RobinVonBerg/cic_ffm/report/paper/main.tex

\documentclass[11pt,oneside,headsepline,a4paper,ngerman]{scrreprt}

% PACKAGES
\usepackage{graphicx}              % images
\usepackage{xcolor}                % colors
\usepackage{tabularx}              % tables
\usepackage{scrlayer-scrpage}      % KOMA-Skript
\usepackage{minted}                % code formatting
\usepackage{scrhack}               % suppress deprecation warnings
\usepackage[utf8]{inputenc}        % encoding translation 
\usepackage{csquotes}              % quotations   
\usepackage{isodate}               % dates
\usepackage{makecell}              % format table cells
\usepackage{subcaption}            % figure formatting
\usepackage[ngerman]{babel}        % region specific formatting 
\usepackage[T1]{fontenc}           % font encoding
\usepackage[hidelinks]{hyperref}   % external links
\usepackage[hypcap=false]{caption} % captions
\usepackage[splitrule]{footmisc}   % footnotes
\usepackage[
    backend=biber,
    style=numeric
]{biblatex}                     % manage bibliography
\usepackage[
    a4paper,
    headheight=30pt,
]{geometry}                     % page layout

% VARIABLES
\newcommand{\vcontext}{Softwareprojekt}
\newcommand{\vprof}{Prof. Dr. Ulrich Hoffmann }
\newcommand{\vsubject}{Projektbericht}
\newcommand{\vtitle}{Team Stadt Frankfurt}
\newcommand{\vsubtitle}{Cross Innovation Class 2022}
\newcommand{\vauthor}{Sven Hülsen, Robin von Berg}
\newcommand{\vallauthor}{Sven Hülsen, Robin von Berg, Celina Krug, Moritz Hillen,\\Florian Bucher, Maybritt Braun, Lucas Below}

% STYLE CHANGES
\addtokomafont{pagehead}{\sffamily\color[rgb]{0.15,0.15,0.15}} 
\addtokomafont{pagefoot}{\sffamily\color[rgb]{0.15,0.15,0.15}} 
\addtokomafont{titlehead}{\sffamily} 
\addtokomafont{subject}{\sffamily} 
\addtokomafont{title}{\sffamily} 
\addtokomafont{subtitle}{\sffamily} 
\addtokomafont{author}{\sffamily} 
\addtokomafont{date}{\sffamily} 
\KOMAoptions{toc=indentunnumbered}

% CAPTION MARGIN
\captionsetup{margin=1.5cm}

% MINTED BACKGROUND COLOR
\definecolor{minted-bg}{rgb}{0.97,0.97,0.97}
% MINTED CONFIG
\setminted {
    bgcolor=minted-bg,
    linenos,
    tabsize=2,
    breaklines
}

\setlength{\parindent}{0pt}

% BIB FILE
\addbibresource{sources.bib}

% HEADER
\ihead*{
    \begin{tabular}{l} 
        \vcontext{} \\
        \vsubtitle{}
    \end{tabular}
}

\rohead*{
    \begin{tabular}{r} 
        \vsubject{} \\
        \vauthor{}
    \end{tabular}
}

% FOOTER
\cfoot*{\thepage}

% DOCUMENT START
\begin{document}

\titlehead{\vcontext{}\\\vprof{}}
\subject{\vsubject{}}
\title{\\\vtitle{}}
\subtitle{\vsubtitle{}}
\author{\vallauthor{}}
\date{\today}

\maketitle

\addtocontents{toc}{~\hfill\textbf{Seite}\par}

\tableofcontents

\input{chapters/00_introduction}
\input{chapters/01_project}
\input{chapters/02_task_determination}
\input{chapters/03_technical_implementation}
\input{chapters/04_result}
\input{chapters/05_conclusion}
\input{chapters/06_summary}

% BIBLIOGRAPHY LINEBREAKS
\setcounter{biburlnumpenalty}{8000}

\printbibliography{}

\listoffigures{}

\end{document}
