RobinVonBerg/cic_ffm/report/paper/chapters/02_task_determination.tex

\chapter{Aufgabenverteilung}

    Während der KickOff Veranstaltung haben wir Personen festgelegt die die Rollen der Projektleitung und die der Außenkommunikation übernehmen. Im Laufe des Projekts wurden diese Aufgaben aber auch von anderen Personen übernommen, sei es wegen Krankheit, anderen Abwesenheiten oder wegen der Menge an Aufgaben.

    \begin{table}[H]
        \centering
        \begin{tabularx}{\textwidth}{ | l | X | }
            \hline
                \textbf{Rolle} & \textbf{Person} \\
            \hline
                Projektleiterin & Celina Krug \\ 
            \hline
                Außenkommunikation & Florian Bucher \\ 
            \hline
        \end{tabularx}
        \caption{Übersicht der intern vergebenen Rollen.}
        \label{table:roles}
    \end{table}

    \begin{table}[H]
        \centering
        \begin{tabularx}{\textwidth}{ | l | X | }                
            \hline
                \textbf{Aufgabe} & \textbf{Person(en)} \\
            \hline
                Löten der technischen Komponenten &  \makecell[l]{Robin, Sven,Celina,\\Moritz} \\ 
            \hline
                Bau der Kabel(bäume) &  Robin, Sven, Moritz \\ 
            \hline
                Modellbau des großen Modells & \makecell[l]{May, Lucas, Annika,\\ Sven, Celina, Moritz,\\Robin} \\ 
            \hline
                Modellbau der zwei kleinen Modelle & \makecell[l]{May, Lucas, Annika,\\Sven, Moritz} \\ 
            \hline
                Implementation \& Kalibrierung des Füllstandssensor & Sven \\
            \hline
                Implementation \& Kalibrierung des dTOF-Sensors & Sven \\
            \hline
                Implementation der Main-dTOF & Sven \\
            \hline
                Implementation der Animationen & Robin \\
            \hline
                Implementation der BLE-Kommunikation & Robin \\
            \hline
                Implementation der Main-Receiver \& Main-Transmitter & Robin \\
            \hline
                Vorbereitung \& Präsentieren Abschlussveranstaltung & Celina, May \\
            \hline
                Kommunikation/Absprachen mit den Praxispartnern & Robin, Florian \\
            \hline
                Teilnahme an den CheckIns & Celina \\
            \hline
        \end{tabularx}
        \caption{Retrospektiv: Welche Aufgaben wurden von wem übernommen.}
        \label{table:detailed_task_}
    \end{table}
