RobinVonBerg/cic_ffm/report/paper/media/01_project/pencil_sketch_bin_1.jpg

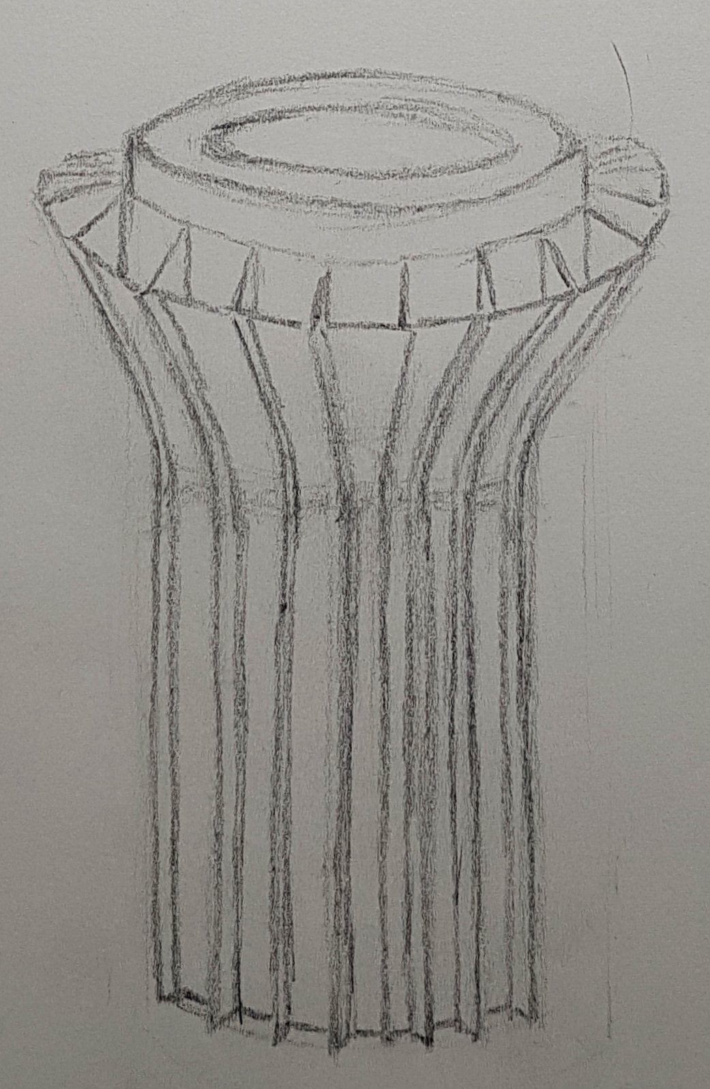
report/paper/media/01_project/pencil_sketch_bin_1.jpg
