RobinVonBerg/cic_ffm/report/paper/media/01_project/WKW_erklaerung.png

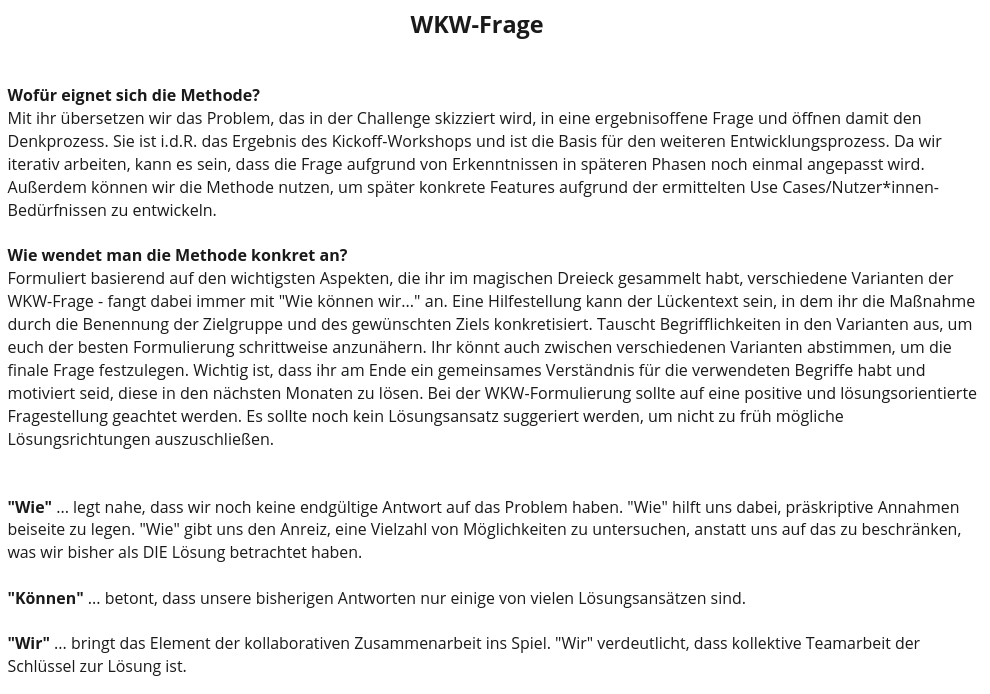
report/paper/media/01_project/WKW_erklaerung.png
