RobinVonBerg/cic_ffm/report/paper/media/01_project/WKW_fragen.png

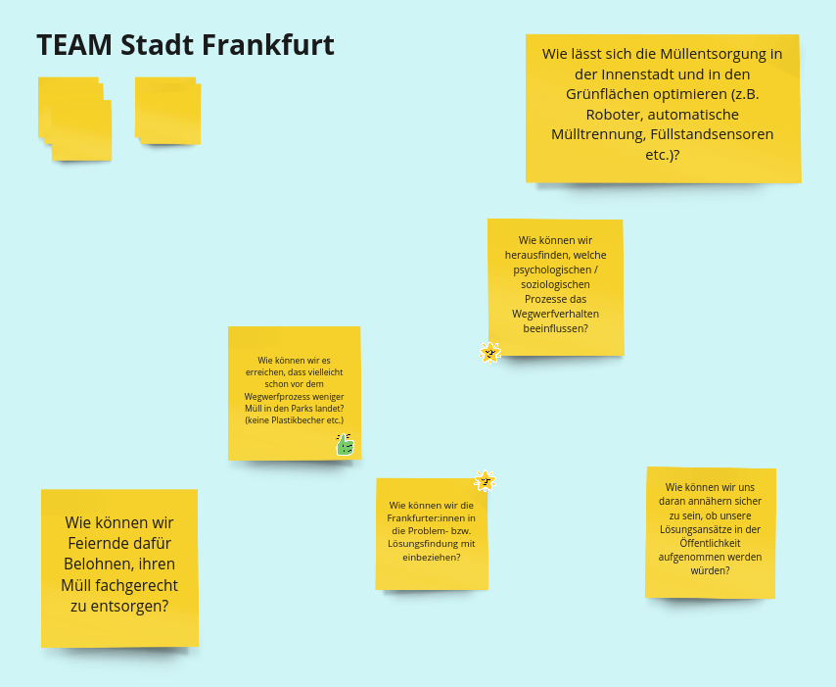
report/paper/media/01_project/WKW_fragen.png
