RobinVonBerg/cic_ffm/report/paper/media/03_technical_implementation/header_2.png

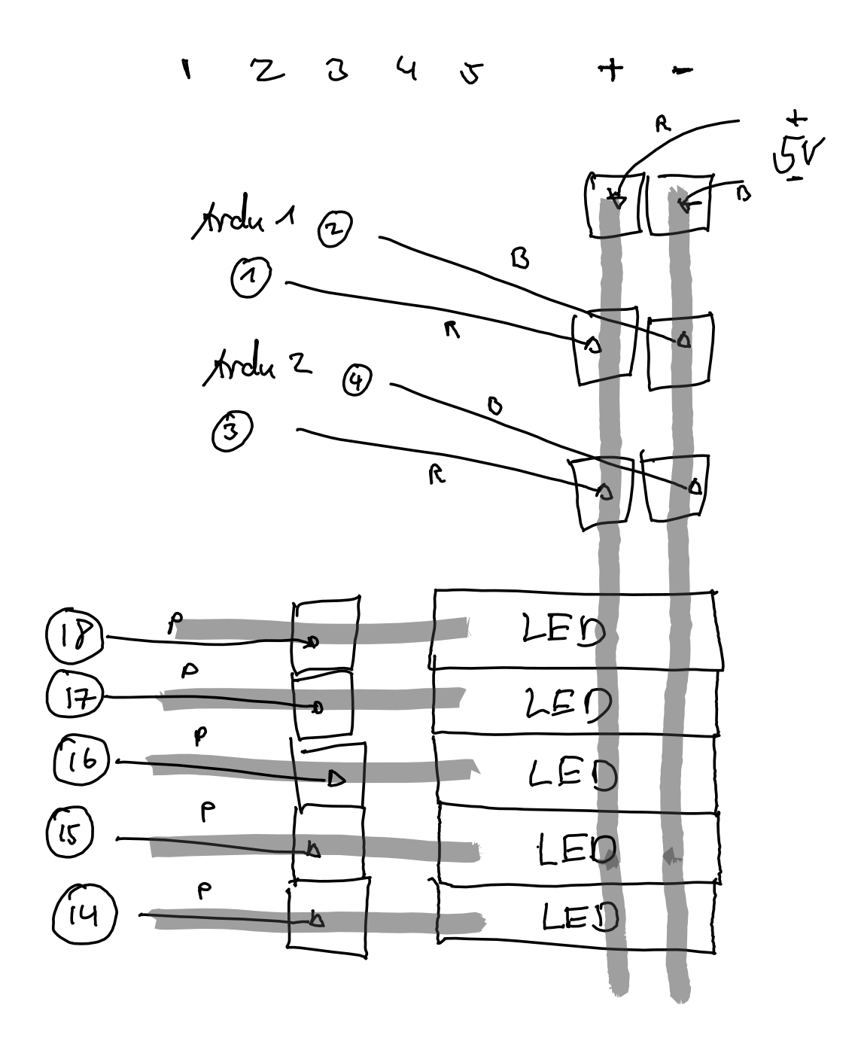
report/paper/media/03_technical_implementation/header_2.png
