RobinVonBerg/cic_ffm/report/paper/media/03_technical_implementation/header_3.png

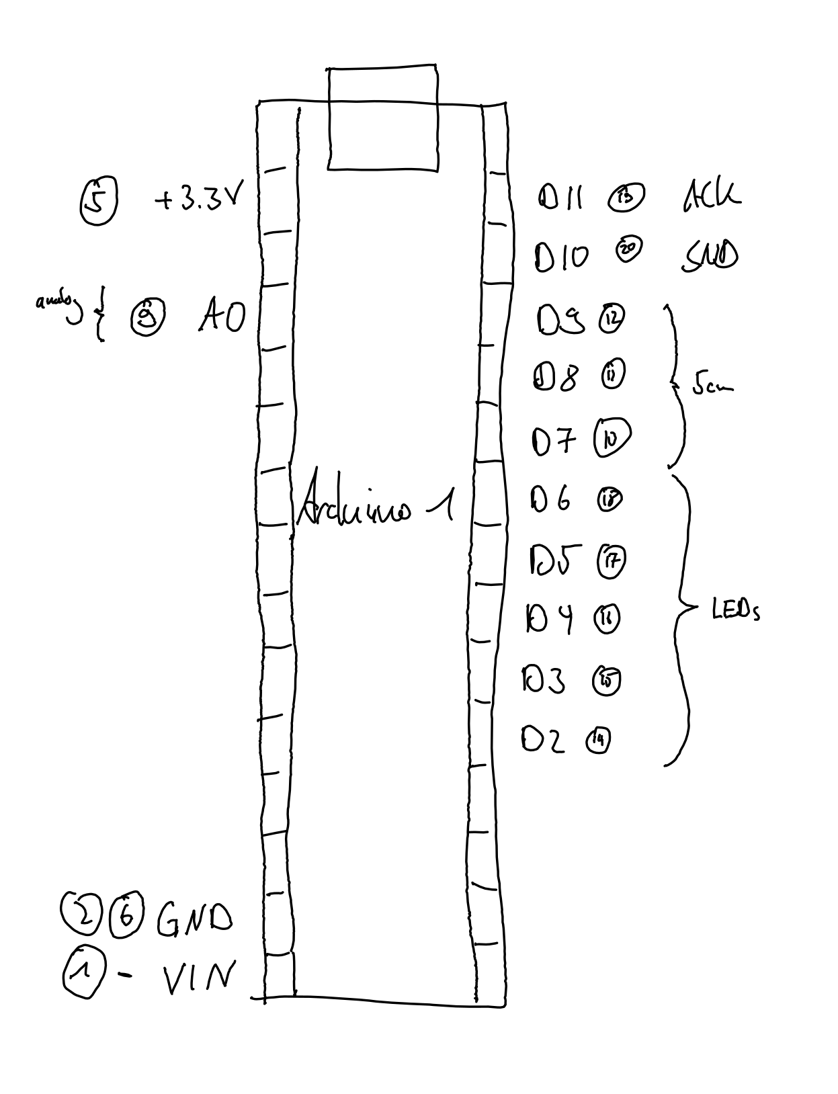
report/paper/media/03_technical_implementation/header_3.png
