RobinVonBerg/cic_ffm/report/paper/media/03_technical_implementation/leds_1.png

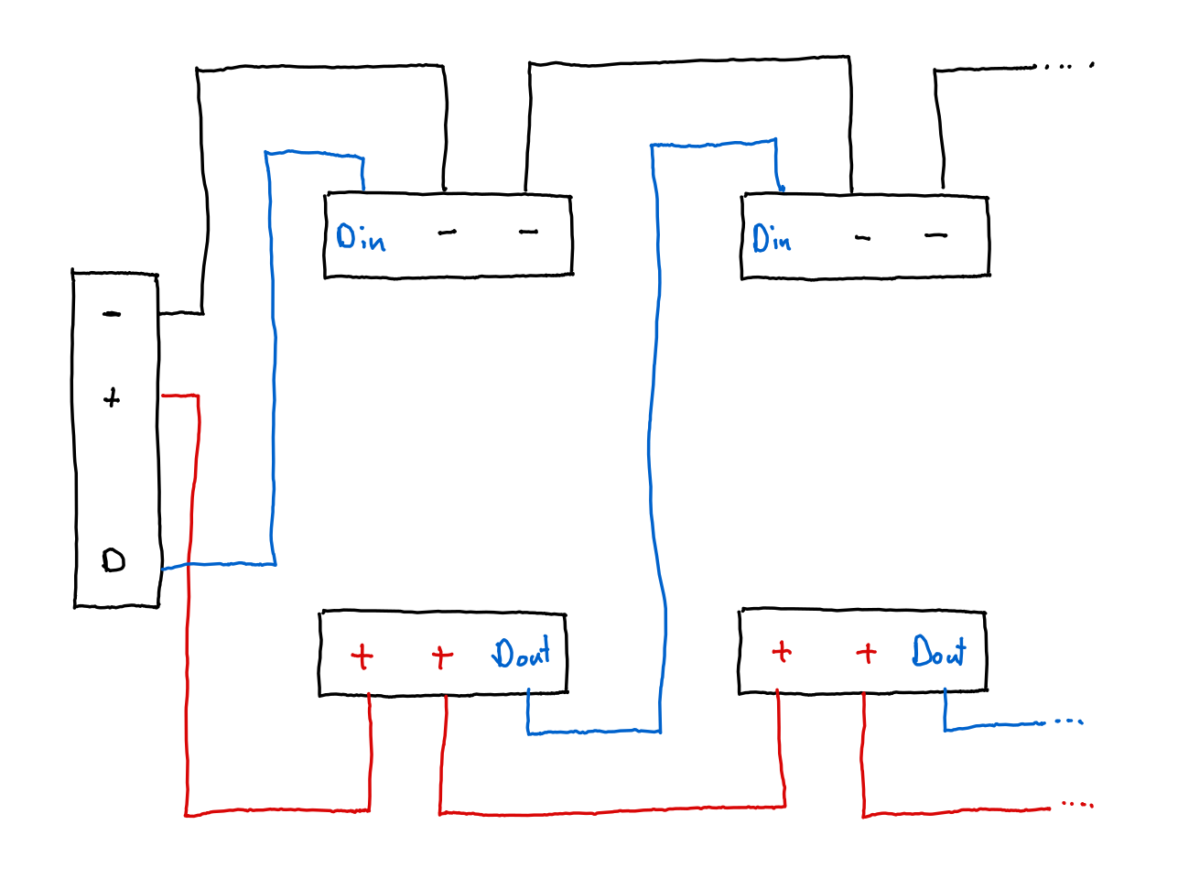
report/paper/media/03_technical_implementation/leds_1.png
