RobinVonBerg/cic_ffm/report/paper/media/03_technical_implementation/sketch_sensor_radius.png

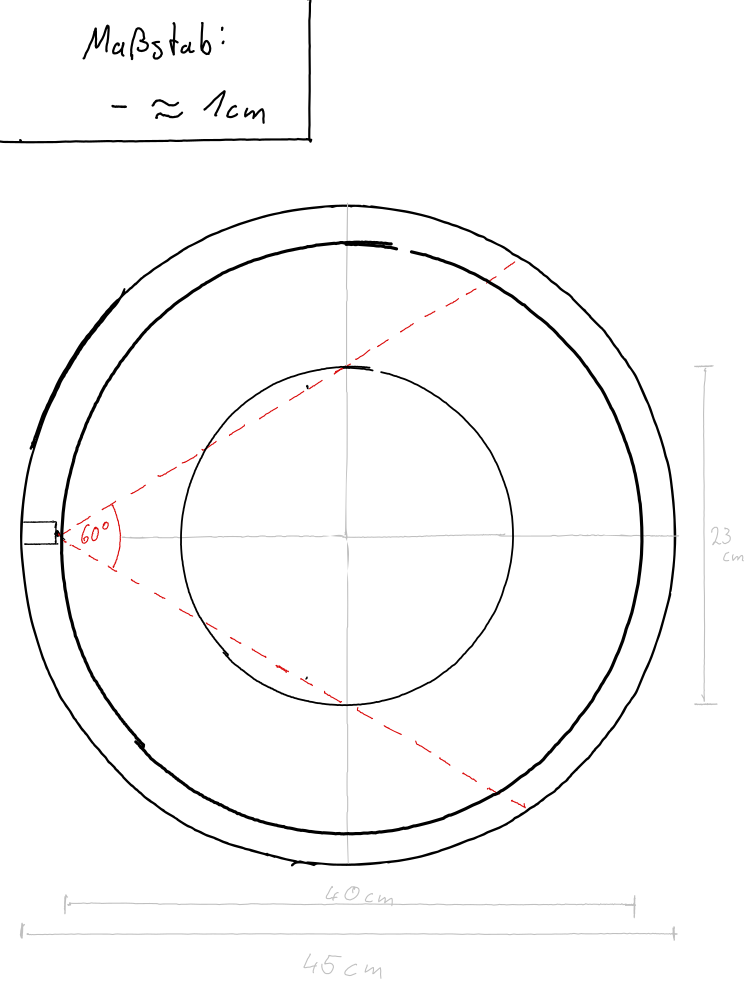
report/paper/media/03_technical_implementation/sketch_sensor_radius.png
