RobinVonBerg/cic_ffm/report/paper/media/04_result/whole_cic.jpg

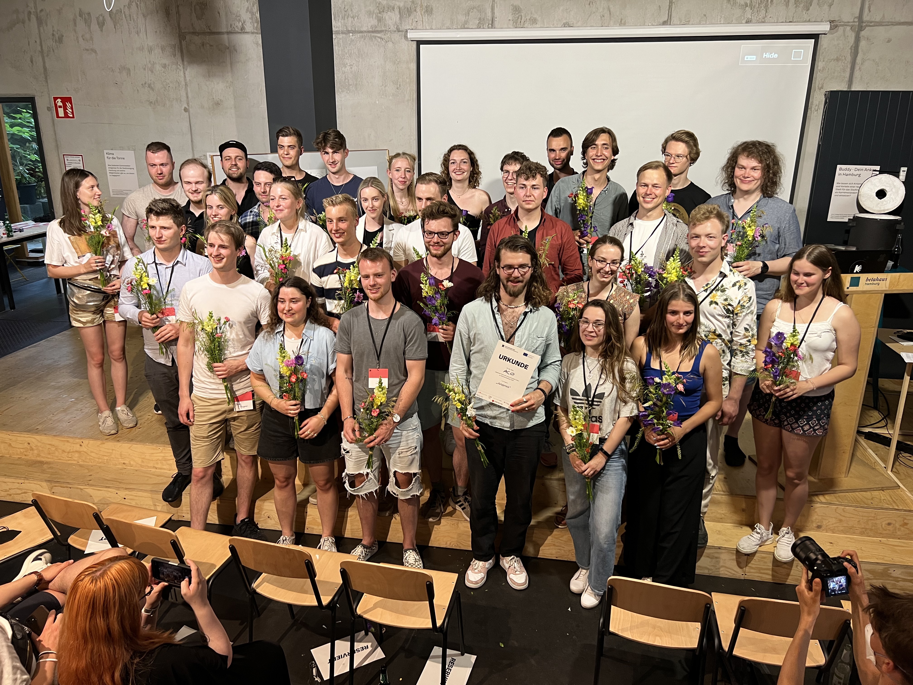
report/paper/media/04_result/whole_cic.jpg
