RobinVonBerg/cic_ffm/arduino/src/animations.hpp

/**
 * @file animations.hpp
 * @author Sven Hülsen (inf104302), Robin von Berg (inf104426)
 * @brief animation data in flash memory.
 */

#pragma once

/* ------ Custom Headers ------ */
#include <types.hpp>

/* ------ Makros ------ */
/**
 * @brief Highest amount of frames an animation is using.
 */
#define MAX_ANIMATION_LENGTH_DS 44

/* ------ Global Variables ------ */

/**
 * @brief Animation durations in miliseconds.
 * 
 */
static const u_int32_t ANIMATION_DURATIONS_MS[META_AMOUNT_ANIMATIONS] = {
    4400, 4400, 4400
};

/**
 * @brief Colorvalues (RGB) of given animation
 *        Are stored in flash memory with a resolution of 10 fps.
 *        
 *        Each row describes an animation frame
 *        and holds a color value for each possible height.
 */
static PROGMEM uint32_t ANIMATIONS[META_AMOUNT_ANIMATIONS][AMOUNT_LED_LAYERS * MAX_ANIMATION_LENGTH_DS] = 
{
    {
        512, 512, 512, 512, 512, 512, 512, 512, 512, 512, 512, 512, 512, 512, 512, 512, 512, 512, 512, 
        512, 512, 512, 512, 512, 512, 512, 512, 512, 512, 512, 512, 512, 512, 512, 512, 512, 512, 512, 
        1792, 1792, 1792, 1792, 1792, 1792, 1792, 1792, 1792, 1792, 1792, 1792, 1792, 1792, 1792, 1792, 1792, 1792, 1792, 
        10752, 10752, 10752, 10752, 10752, 10752, 10752, 10752, 10752, 10752, 10752, 18688, 18688, 18688, 18688, 18688, 29952, 44544, 62720, 
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

/* ---- Methods ---- */

/**
 * @brief Returns the duration in miliseconds for the given animation.
 */
DurationMS getAnimationDuration(AnimationType animation);

/**
* @brief Returns the (flash memory) pointer for the given animation.
*/
uint32_t* getAnimationPointer(AnimationType animation);
